paulmandal/radio-adapter/ucontroller-code/message_buffer.h

/**
 * Message buffer for serial input
 */
#ifndef MessageBuffer_h
#define MessageBuffer_h

class MessageBuffer {
  public:
    MessageBuffer(int bufferSize);
    void write(char c);
    void copyTo(volatile MessageBuffer &dest);
    char *getMessage();
    void clear();
    int length();
  private:
    int _bufferPosition;
    int _bufferSize;
    char *_msgBuffer;
};

#endif
